JOM52/esp32-airsens-v2/schema/airsens_v1_0.kicad_sch

## KiCad design schema/airsens_v1_0.kicad_sch (2023-04-16)

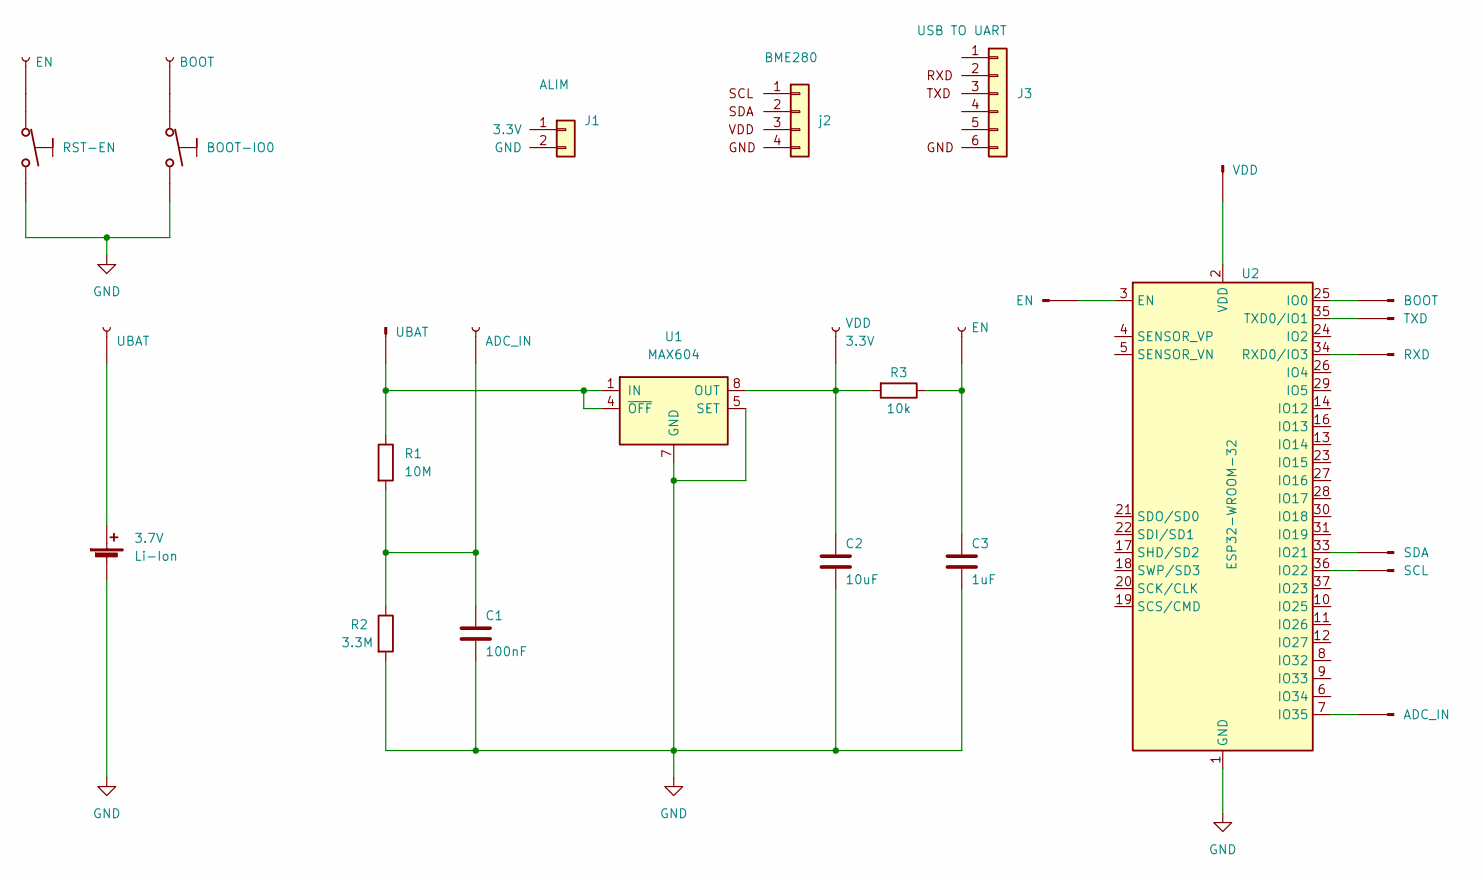
[picture p5: schematic airsens_v1_0.kicad_sch]

Parts:
3.7V: Li-Ion
BOOT: EN
C1: 100nF
C2: 10uF
C3: 1uF
EN: EN
J1: ALIM
J3: USB TO UART
R1: 10M
R2: 3.3M
R3: 10k
U1: MAX604
U2: ESP32-WROOM-32
VDD: 3.3V
j2: BME280

Connections:
unnamed: C1.1, R1.2, R2.1
unnamed: C1.2, C2.2, C3.2, R2.2, U1.2 (GND), U1.3 (GND), U1.5 (SET), U1.6 (GND), U1.7 (GND)
unnamed: C2.1, R3.2, U1.8 (OUT), VDD.1
unnamed: C3.1, EN.1, R3.1
unnamed: R1.1, U1.1 (IN), U1.4 (~OFF)
unnamed: U2.1 (GND), U2.15 (GND), U2.38 (GND), U2.39 (GND)
